mhollands/TEP-Lightshow/Gerber/Renders/bottomsilk.png

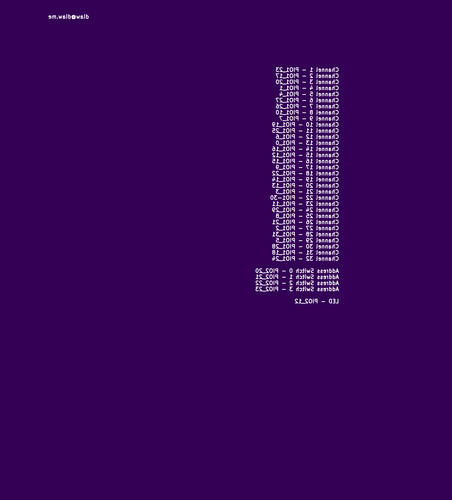
Gerber/Renders/bottomsilk.png
