mhollands/TEP-Lightshow/Gerber/Renders/top.png

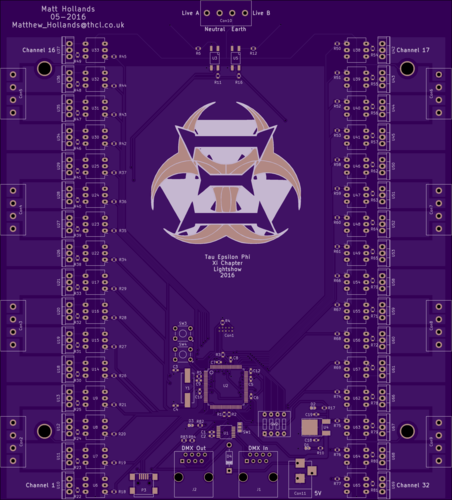
Gerber/Renders/top.png
