mhollands/TEP-Lightshow/Gerber/Renders/topmask.png

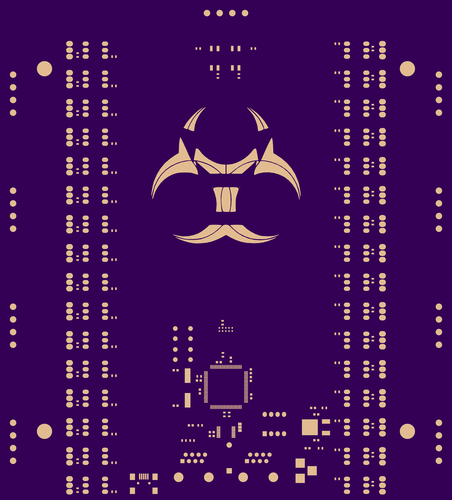
Gerber/Renders/topmask.png
