mhollands/TEP-Lightshow/Gerber/Renders/topsilk.png

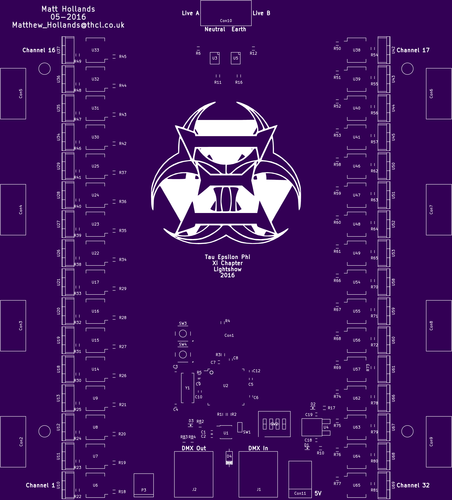
Gerber/Renders/topsilk.png
